speedypotato/SplitFox-Pro/cad/export/rubber/splitfox-foot-2mm.JPG

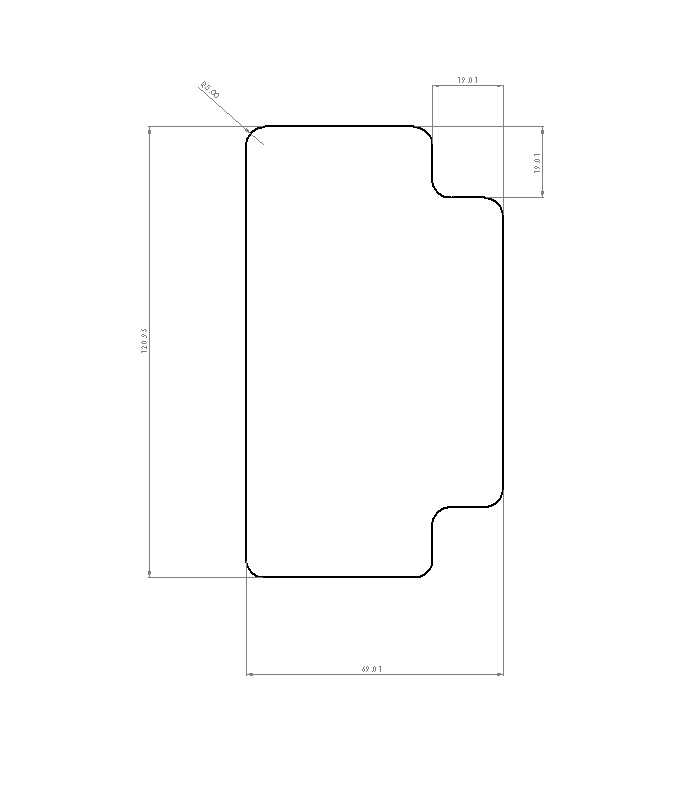
cad/export/rubber/splitfox-foot-2mm.JPG
