speedypotato/SplitFox-Pro/cad/export/rubber/splitfox-foot-2mm.png

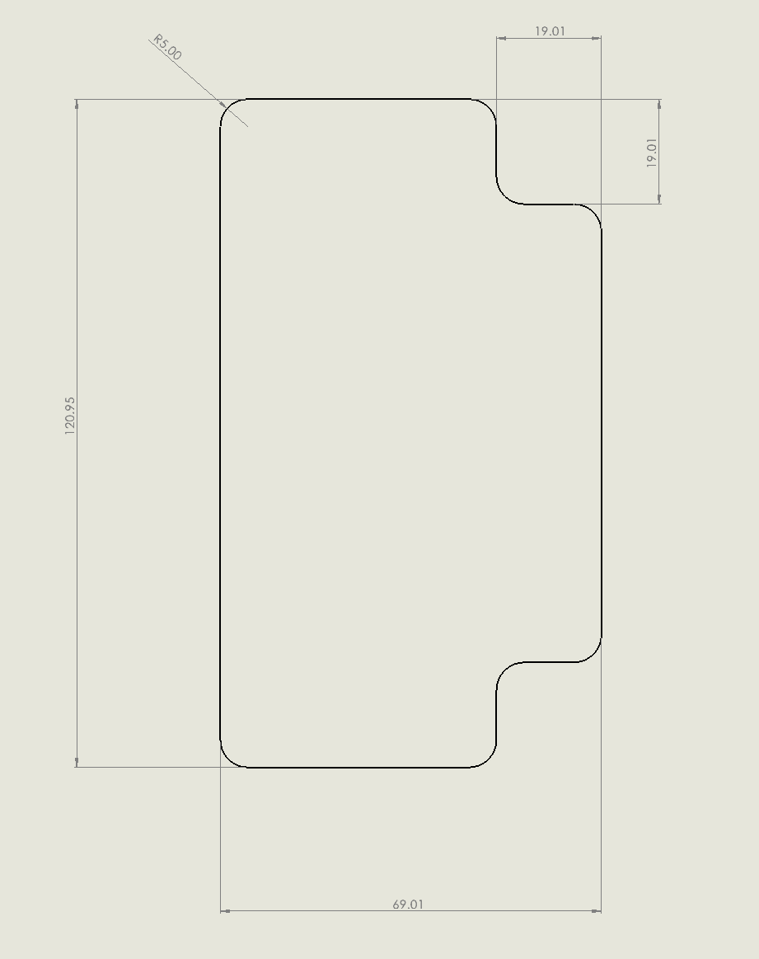
cad/export/rubber/splitfox-foot-2mm.png
