speedypotato/SplitFox-Pro/pcb/DRC.png

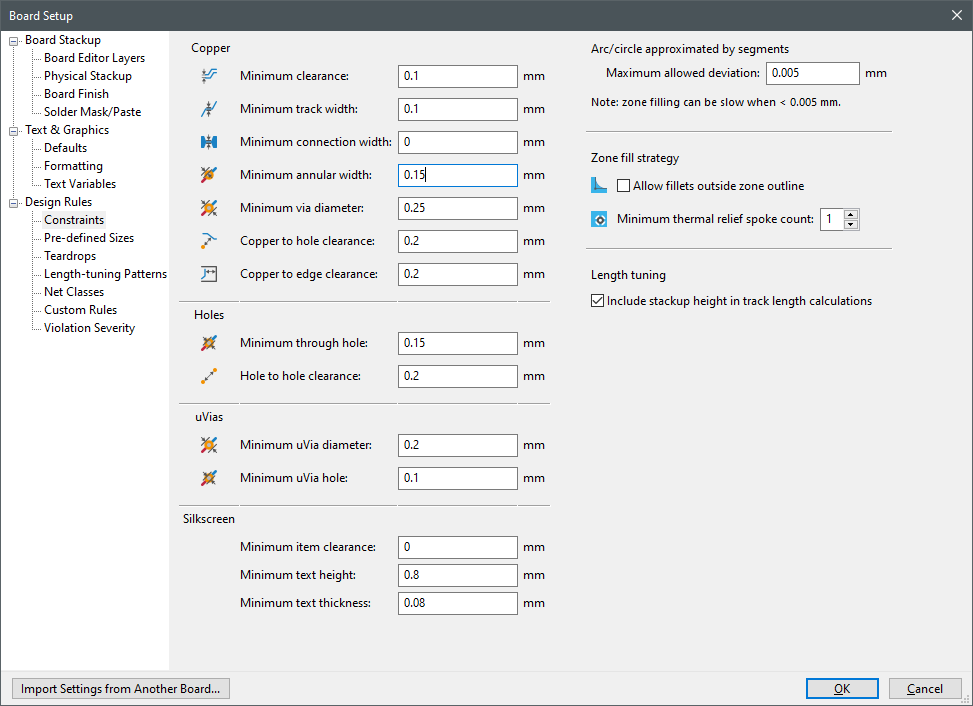
pcb/DRC.png
