speedypotato/SplitFox-Pro/video/screenshots/1_github.png

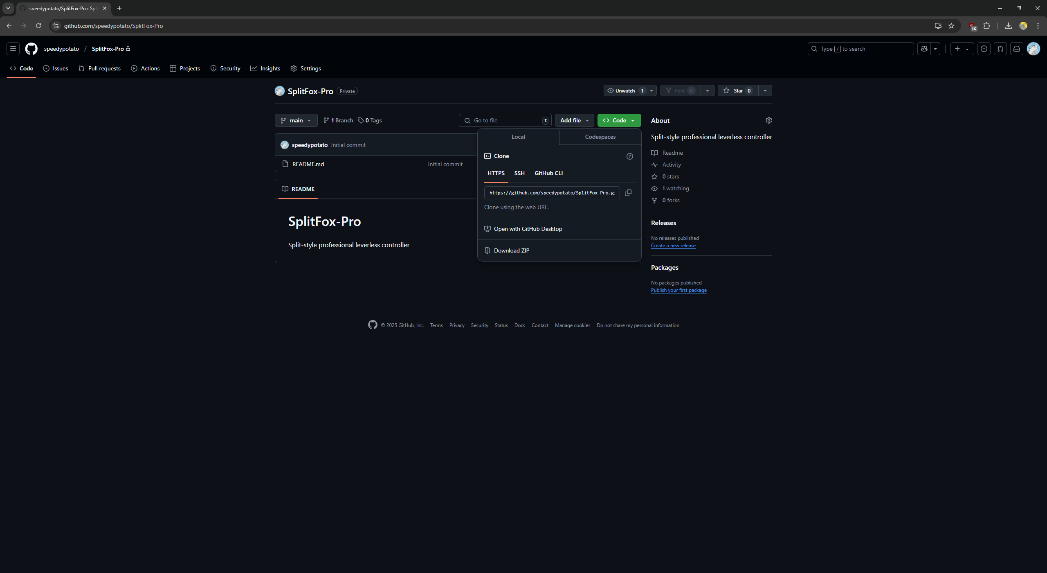
video/screenshots/1_github.png
