speedypotato/SplitFox-Pro/video/screenshots/2_slagcoin.png

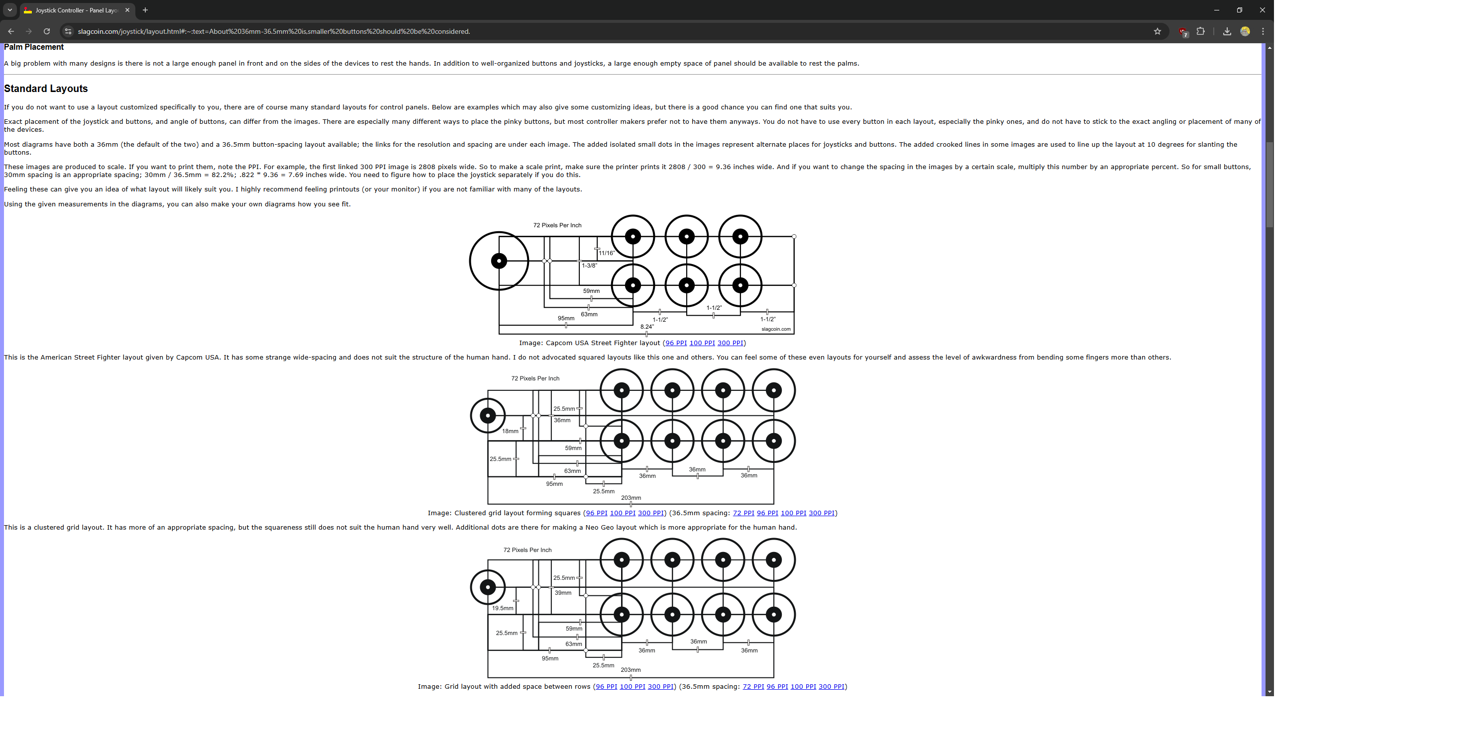
video/screenshots/2_slagcoin.png
