speedypotato/SplitFox-Pro/cad/3d-print-test/splitfox-foot.3MF

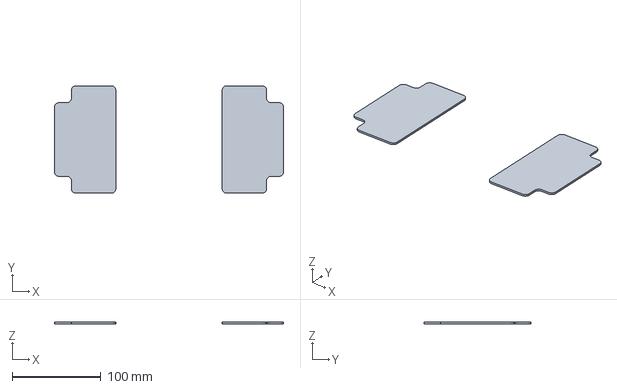
[picture p28: CAD file, 2025-03-01]
cad/3d-print-test/splitfox-foot.3MF
257.8 x 121.0 x 2.00 mm
