speedypotato/SplitFox-Pro/cad/export/acrylic/splitfox-bottom.STEP

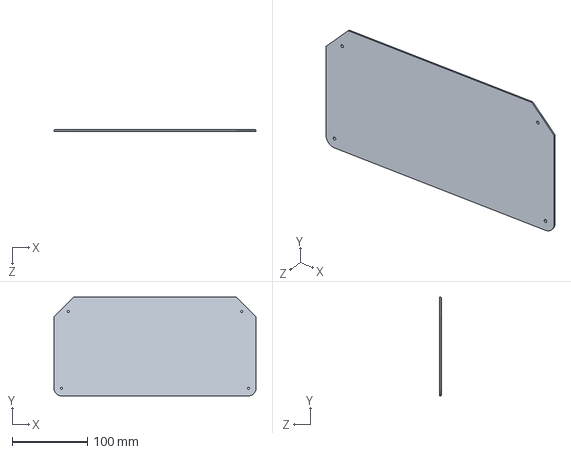
[picture p29: CAD file, 2025-03-10]
cad/export/acrylic/splitfox-bottom.STEP
267.8 x 131.0 x 2.50 mm
