speedypotato/SplitFox-Pro/cad/export/aluminum/splitfox-wasd-m-1_2mm.DXF

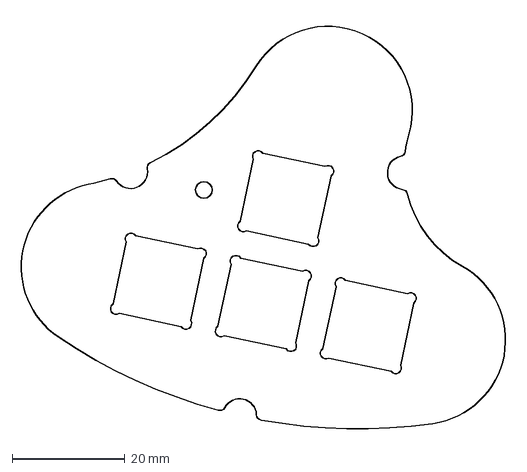
[picture p30: CAD file, 2025-03-10]
cad/export/aluminum/splitfox-wasd-m-1_2mm.DXF
87.8 x 73.8 mm
