speedypotato/SplitFox-Pro/cad/parts/1u.SLDPRT

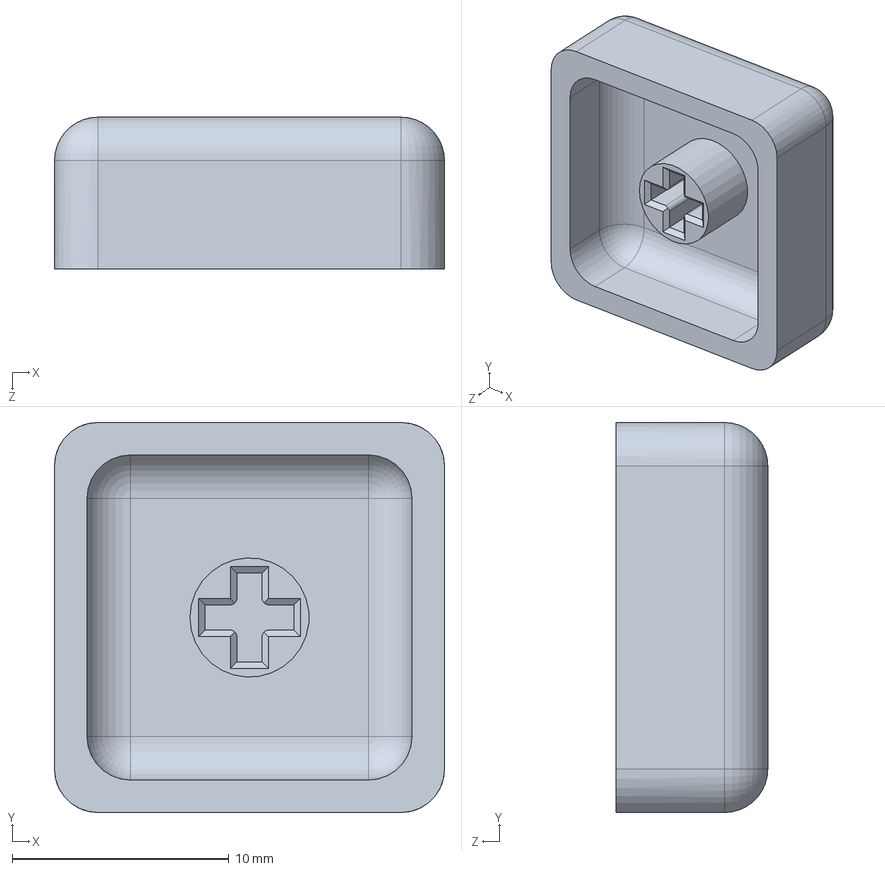
[picture p31: CAD file, 2025-02-13]
cad/parts/1u.SLDPRT
18.0 x 18.0 x 7.00 mm
