speedypotato/SplitFox-Pro/cad/usb-ext-top.SLDPRT

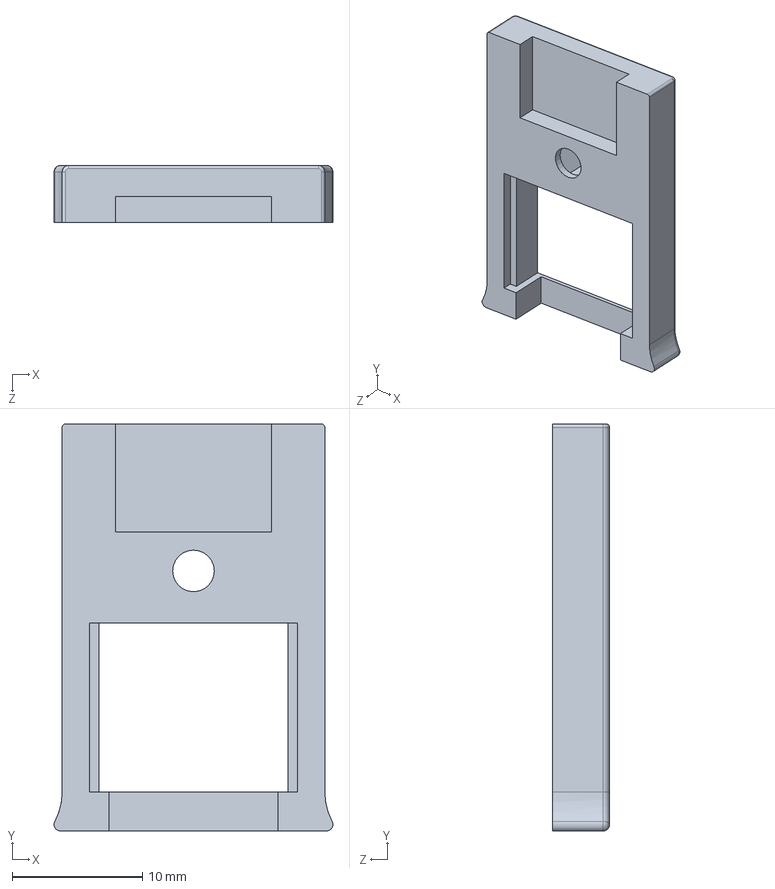
[picture p32: CAD file, 2025-03-11]
cad/usb-ext-top.SLDPRT
21.4 x 31.3 x 4.40 mm
