speedypotato/SplitFox-Pro/pcb/wasd-m/wasd-m.step

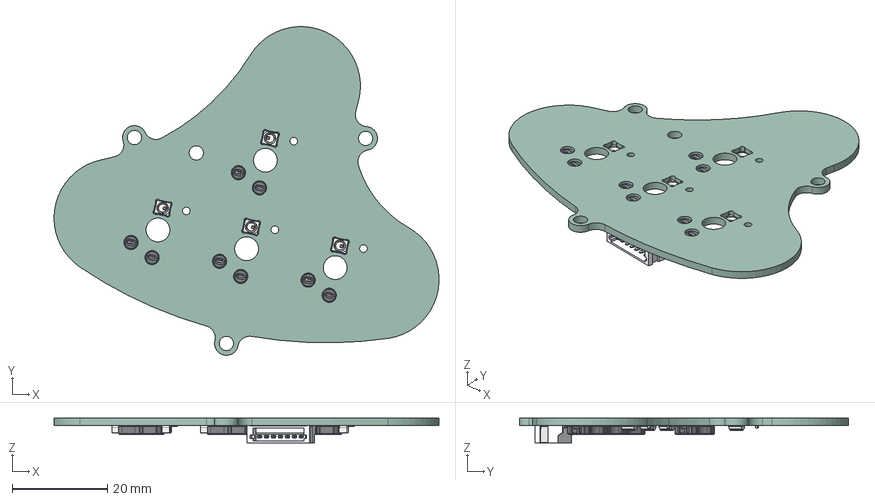
[picture p33: CAD file, 2025-02-12]
pcb/wasd-m/wasd-m.step
81.0 x 69.1 x 5.25 mm
HS_Kailh_Choc v4 x 4
LED_SK6812MINI-E v2 x 4
C_0402_1005Metric x 4
CONN-SMD_S7B-ZR-SM4A-TF-LF-SN
_autosave-wasd-m_PCB
