speedypotato/SplitFox-Pro/cad/3d-print-test/splitfox-top.DXF

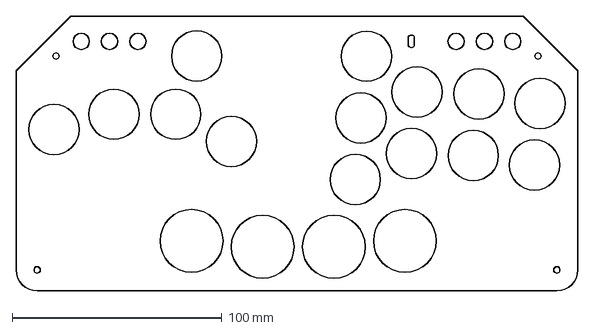
[picture p34: CAD file, 2025-02-15]
cad/3d-print-test/splitfox-top.DXF
267.8 x 131.0 mm
