speedypotato/SplitFox-Pro/cad/export/aluminum/splitfox-body.STEP

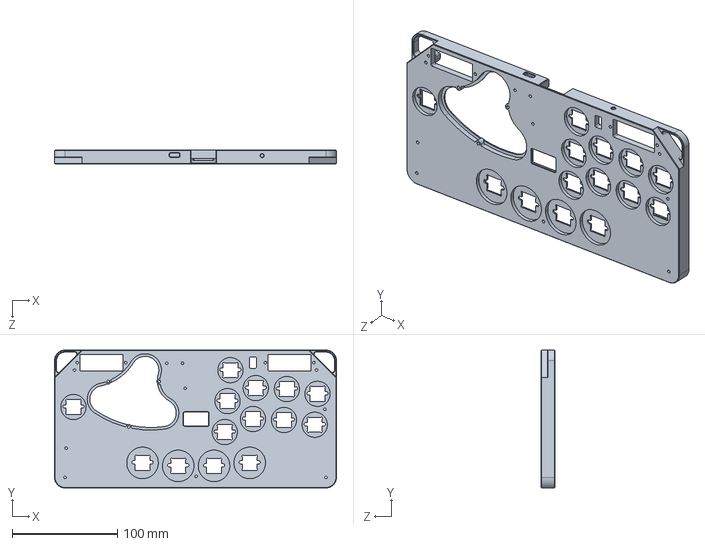
[picture p35: CAD file, 2025-03-10]
cad/export/aluminum/splitfox-body.STEP
267.8 x 131.0 x 13.0 mm
