speedypotato/SplitFox-Pro/cad/parts/concave_22-5.SLDPRT

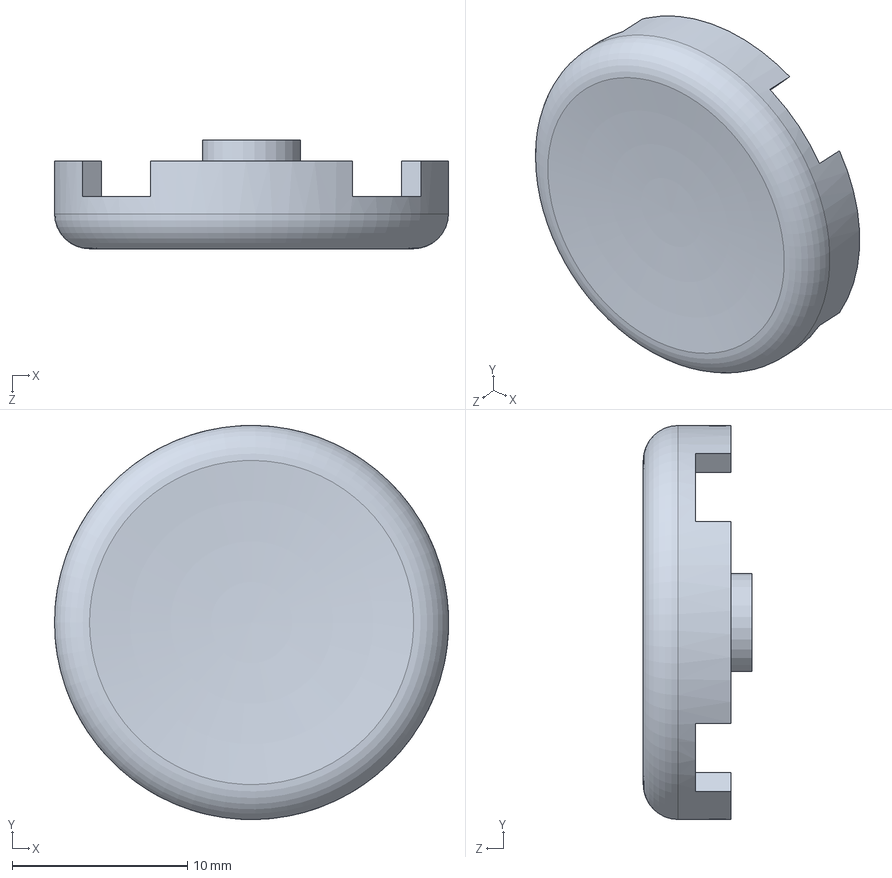
[picture p36: CAD file, 2025-02-12]
cad/parts/concave_22-5.SLDPRT
22.5 x 22.5 x 6.20 mm
