speedypotato/SplitFox-Pro/cad/usb-ext-bot.SLDPRT

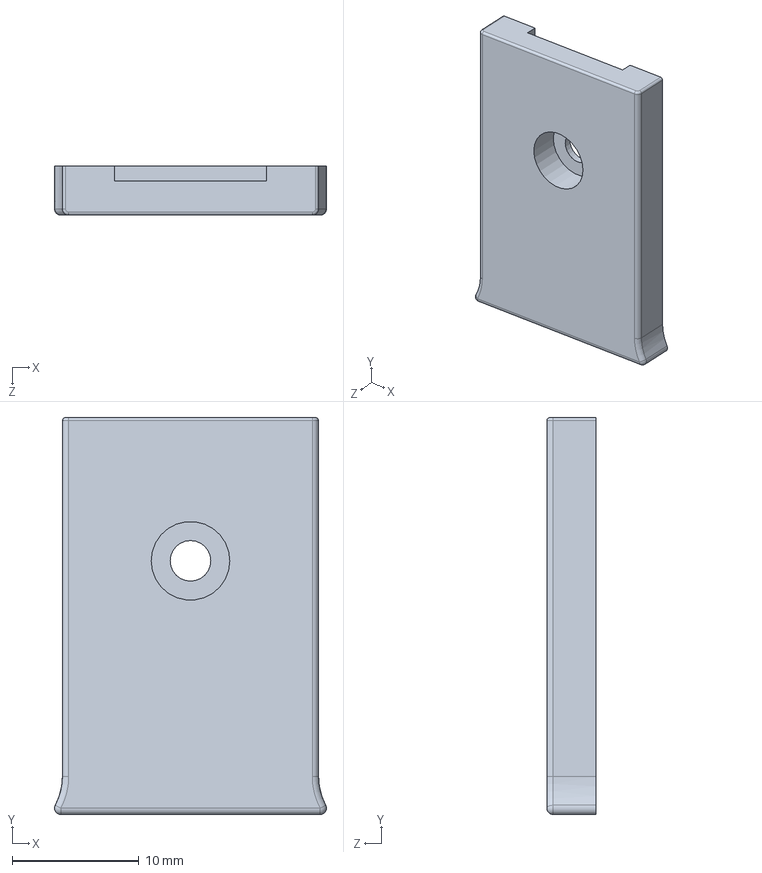
[picture p37: CAD file, 2025-03-11]
cad/usb-ext-bot.SLDPRT
21.4 x 31.3 x 3.90 mm
