speedypotato/SplitFox-Pro/cad/parts/Kailh_PG1353.SLDPRT

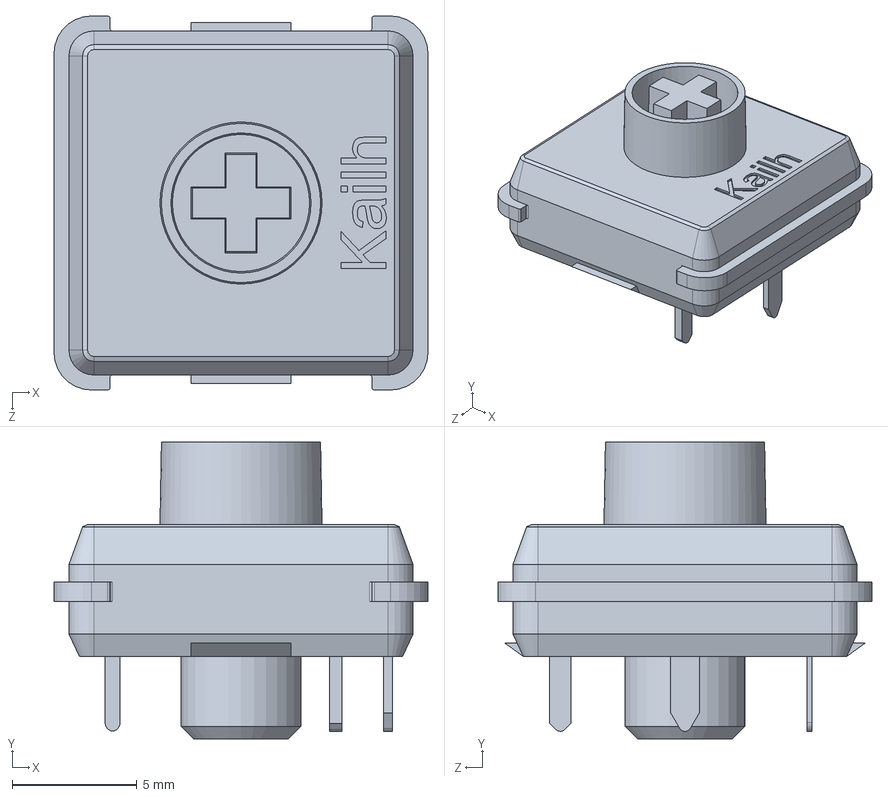
[picture p39: CAD file, 2025-02-12]
cad/parts/Kailh_PG1353.SLDPRT
15.0 x 11.9 x 15.0 mm
