speedypotato/SplitFox-Pro/cad/3d-print-test/splitfox-top-m.DXF

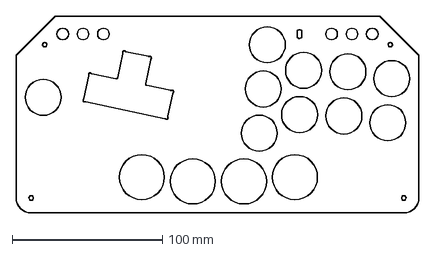
[picture p40: CAD file, 2025-02-15]
cad/3d-print-test/splitfox-top-m.DXF
267.8 x 131.0 mm
