speedypotato/SplitFox-Pro/cad/parts/concave_28-5.SLDPRT

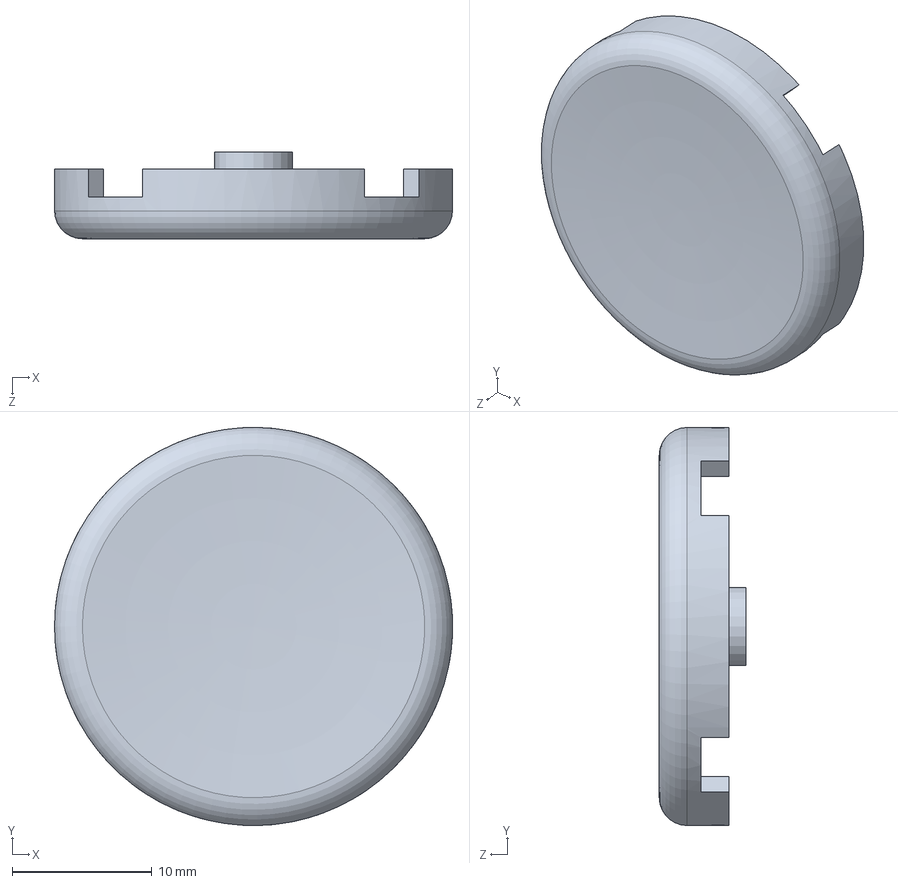
[picture p41: CAD file, 2025-02-12]
cad/parts/concave_28-5.SLDPRT
28.5 x 28.5 x 6.20 mm
