speedypotato/SplitFox-Pro/cad/3d-print-test/splitfox-wasd-m.3MF

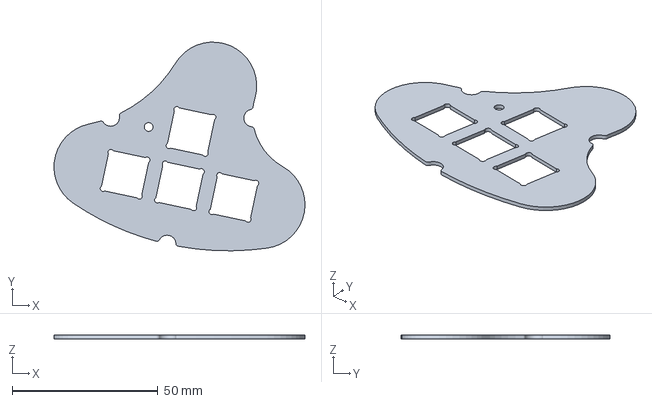
[picture p42: CAD file, 2025-02-14]
cad/3d-print-test/splitfox-wasd-m.3MF
86.0 x 71.5 x 1.20 mm
