speedypotato/SplitFox-Pro/cad/splitfox-top-m-art.DXF

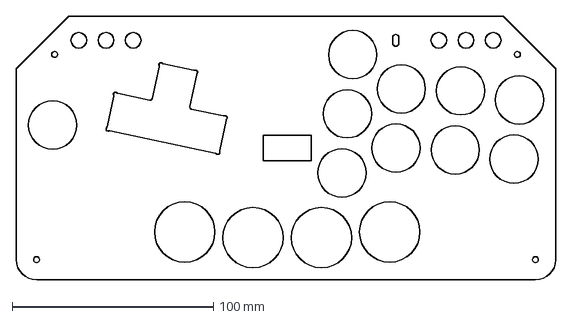
[picture p43: CAD file, 2025-02-15]
cad/splitfox-top-m-art.DXF
267.8 x 131.0 mm
