speedypotato/SplitFox-Pro/cad/parts/honson-f5.SLDPRT

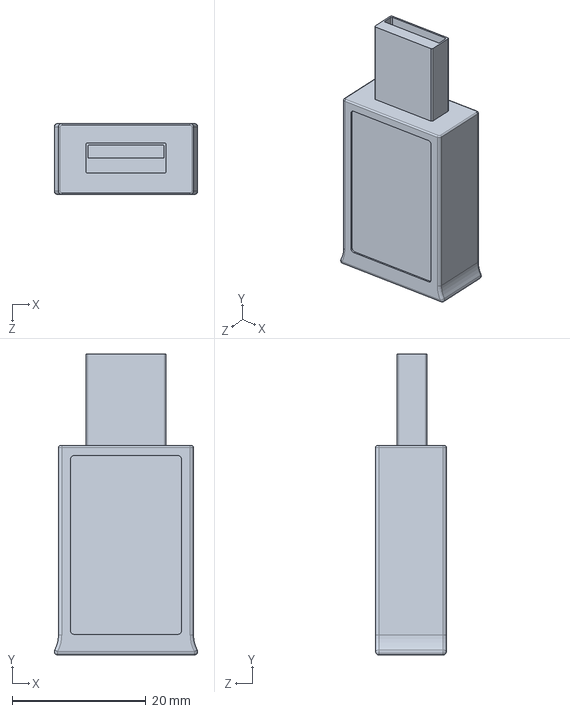
[picture p44: CAD file, 2025-01-30]
cad/parts/honson-f5.SLDPRT
21.4 x 45.0 x 10.6 mm
