speedypotato/SplitFox-Pro/cad/3d-print-test/splitfox-wasd.3MF

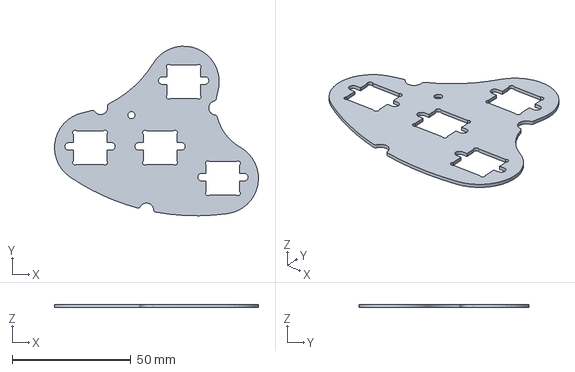
[picture p45: CAD file, 2025-02-13]
cad/3d-print-test/splitfox-wasd.3MF
86.0 x 71.5 x 1.20 mm
