speedypotato/SplitFox-Pro/cad/splitfox-top-art.DXF

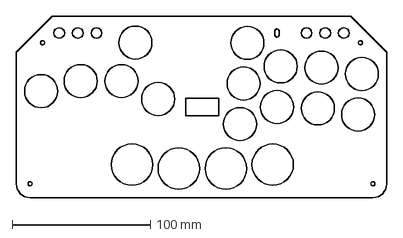
[picture p46: CAD file, 2025-02-15]
cad/splitfox-top-art.DXF
267.8 x 131.0 mm
