speedypotato/SplitFox-Pro/cad/3d-print-test/splitfox-body.SLDPRT

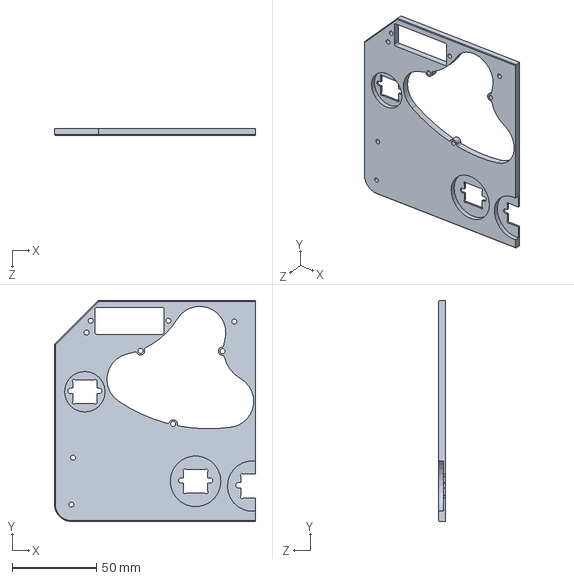
[picture p47: CAD file, 2025-02-13]
cad/3d-print-test/splitfox-body.SLDPRT
119.1 x 131.0 x 4.20 mm
