speedypotato/SplitFox-Pro/cad/pos-splitfox.SLDPRT

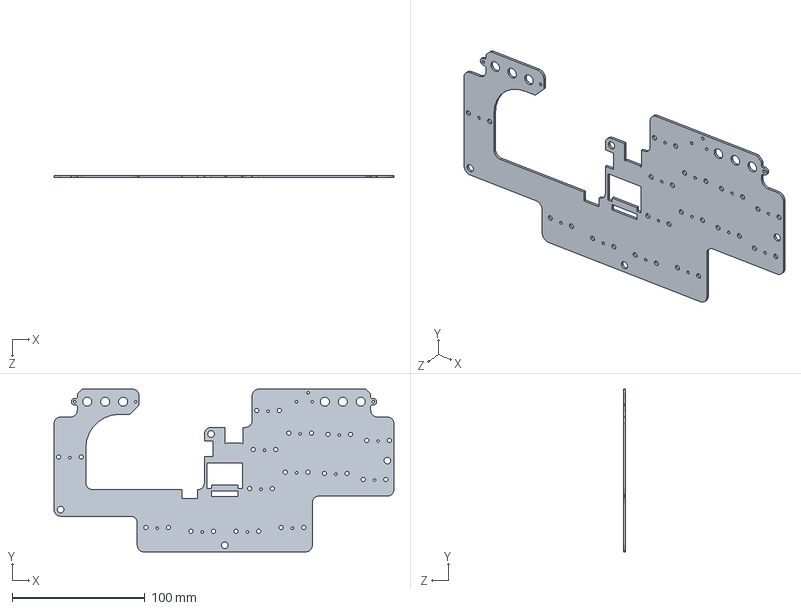
[picture p48: CAD file, 2025-02-10]
cad/pos-splitfox.SLDPRT
255.8 x 122.5 x 1.60 mm
