speedypotato/SplitFox-Pro/cad/pos-wasd-m.SLDPRT

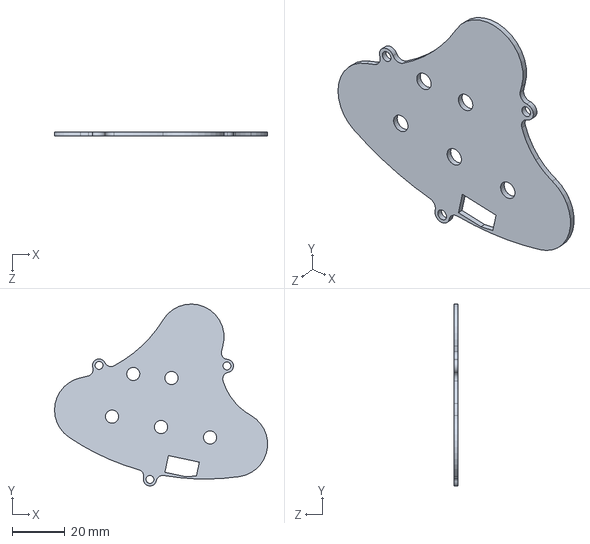
[picture p49: CAD file, 2025-02-03]
cad/pos-wasd-m.SLDPRT
81.0 x 69.1 x 1.60 mm
