speedypotato/SplitFox-Pro/cad/pos-usb.SLDPRT

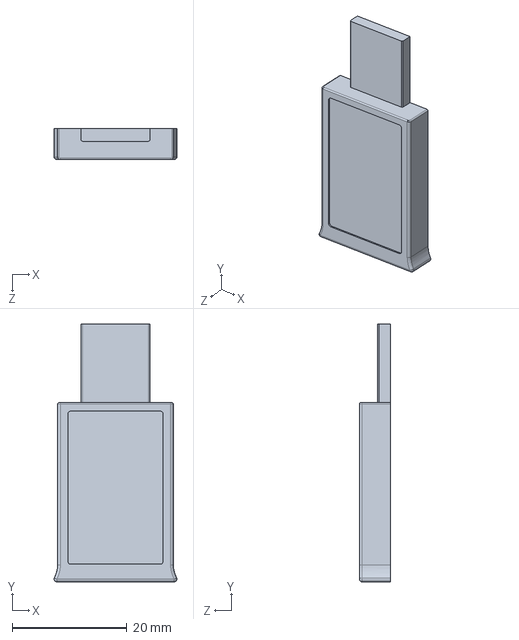
[picture p50: CAD file, 2025-02-03]
cad/pos-usb.SLDPRT
21.4 x 45.0 x 5.45 mm
