speedypotato/SplitFox-Pro/cad/pos-usb-breakout.SLDPRT

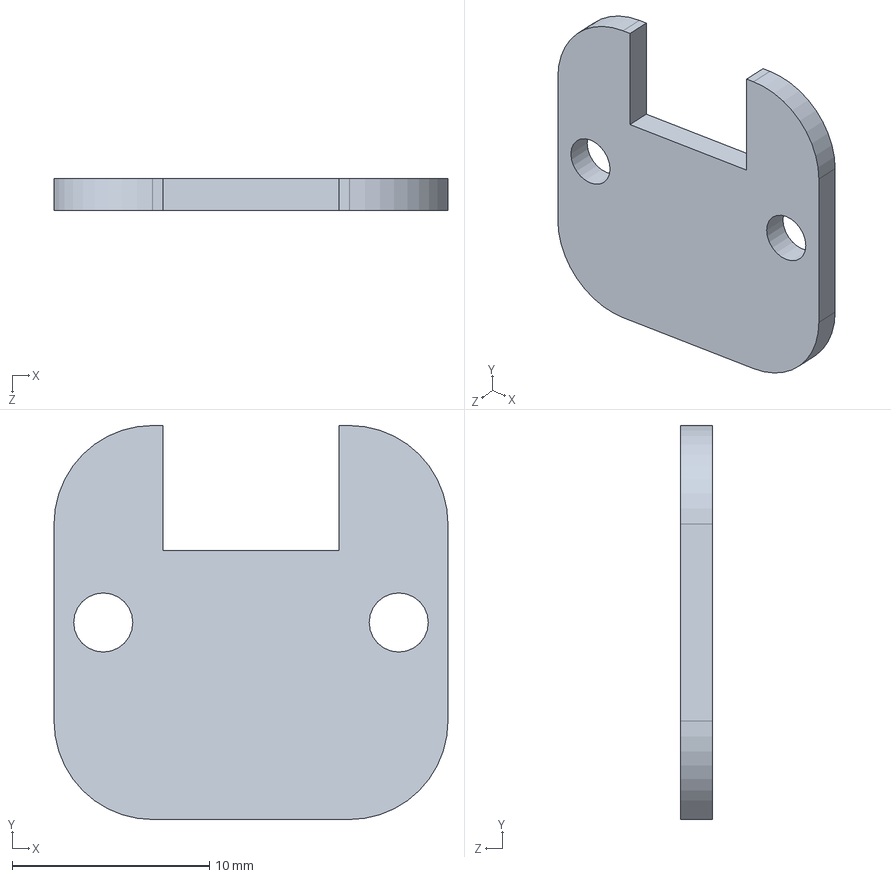
[picture p51: CAD file, 2025-02-02]
cad/pos-usb-breakout.SLDPRT
20.0 x 20.0 x 1.60 mm
