speedypotato/SplitFox-Pro/video/screenshots/4_measure.png

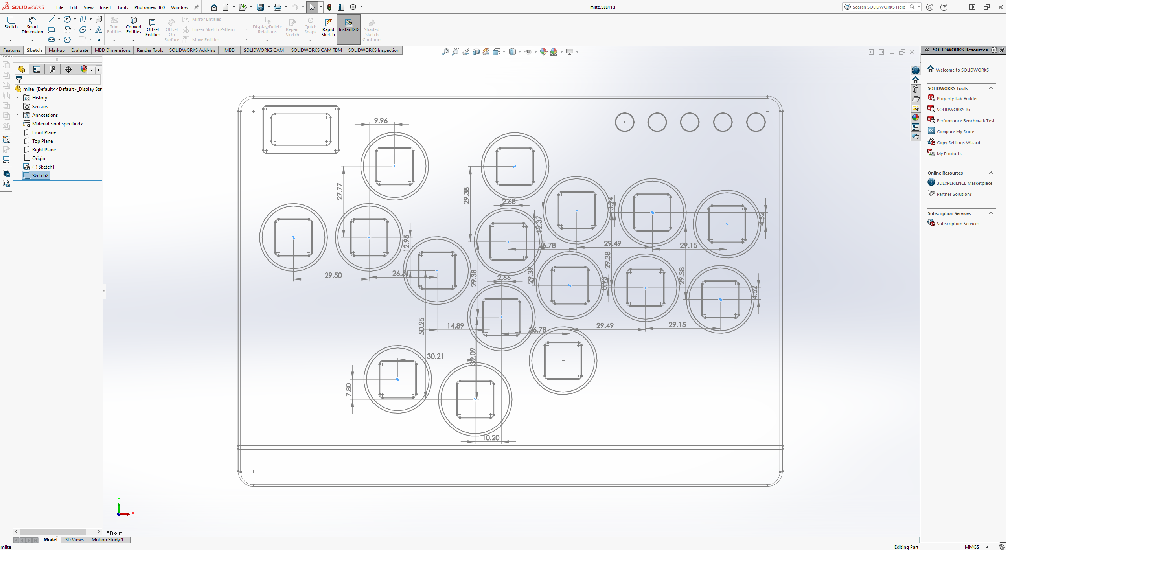
video/screenshots/4_measure.png
